andreasb242/CH55xG-StateLight/Linux/statelight/eeprom_write.py

#!/usr/bin/python3

# Helper to configure Device
# License: GPL
# Author: Andreas Butti

import json
import serial
from struct import pack
import time


def main():
	i = 0
	with open("eeprom.bin", "rb") as file:
		byte = file.read(1)
		while byte != b"":
			print('.', end='', flush=True)
			ok, result = send_command("c%i %i\n" % (i, ord(byte)));
			if result[:2] != "OK":
				print("Failed to write EEPROM at address %d" % i)
				print(">" + result + "<")
				return
			
			i = i + 1
			byte = file.read(1)

	print("\nWriting finished")


def send_command(cmd):
	try:
		serialPort = serial.Serial("/dev/statelight", 9600, timeout=0.1)
	except BaseException as e:
		serialPort = serial.Serial("/dev/ttyACM0", 9600, timeout=0.1)

	result = ""

	try:
		serialPort.write(cmd.encode())
		serialPort.flush()
		time.sleep(0.01)
		result = serialPort.readline().decode().strip()
	except BaseException as e:
		return False, "Exception " + str(e)

	try:
		serialPort.close()
	except BaseException as e:
		return False, "Exception " + str(e)

	return result == "OK", result


if __name__ == "__main__":
	main()
